felipeg86/Easyrun/Images/Aux Pines ESP.JPG

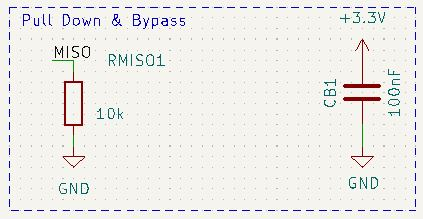
Images/Aux Pines ESP.JPG
