felipeg86/Easyrun/Images/Boost.png

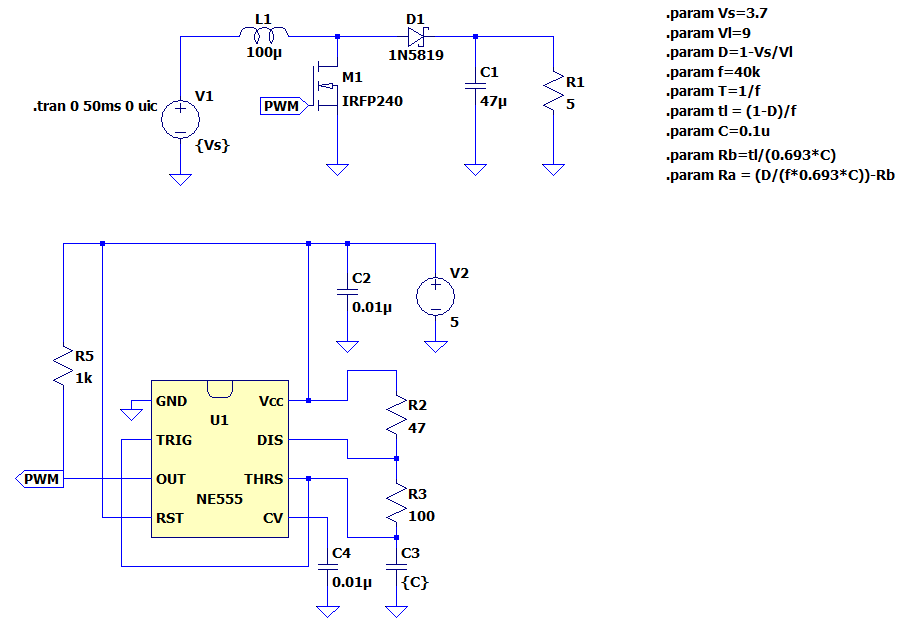
Images/Boost.png
