felipeg86/Easyrun/Images/Botones.JPG

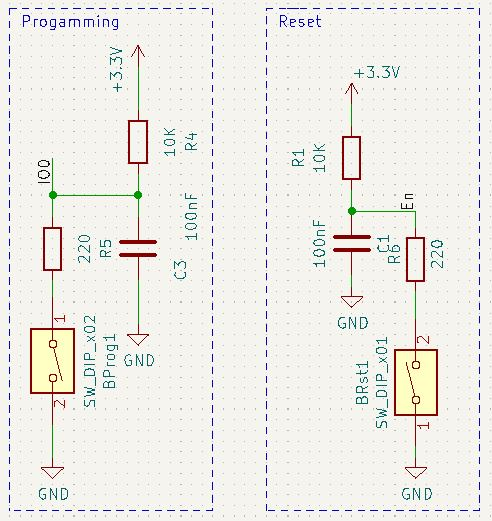
Images/Botones.JPG
