felipeg86/Easyrun/Images/Buck Diagram.png

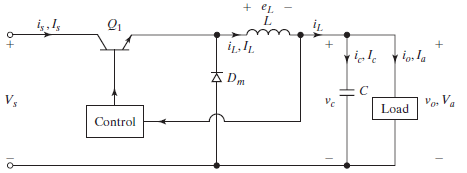
Images/Buck Diagram.png
