felipeg86/Easyrun/Images/Caja candado.jpg

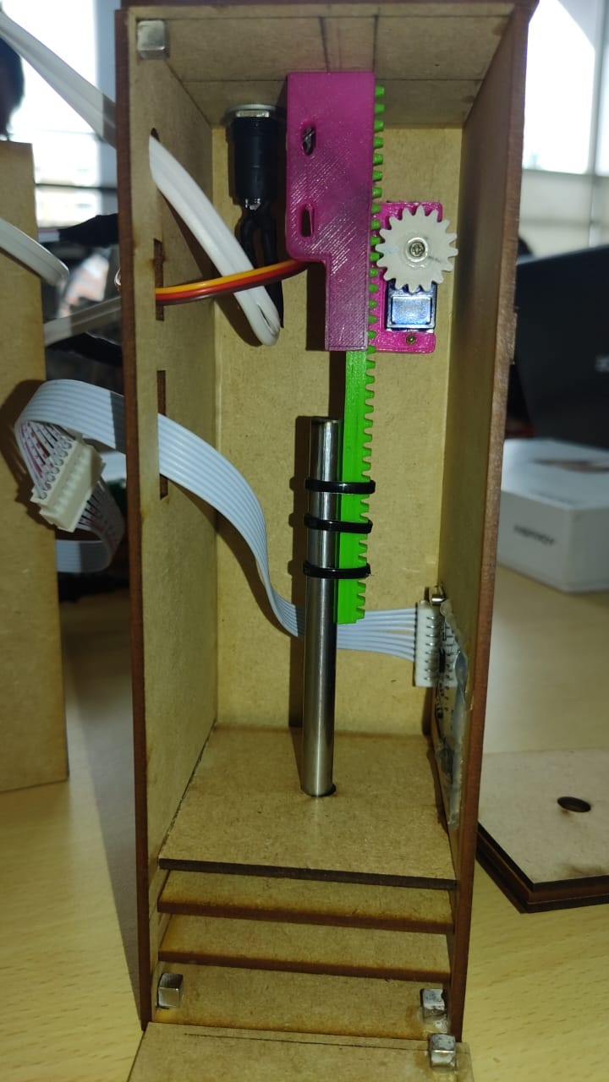
Images/Caja candado.jpg
