felipeg86/Easyrun/Images/caja con pcb.PNG

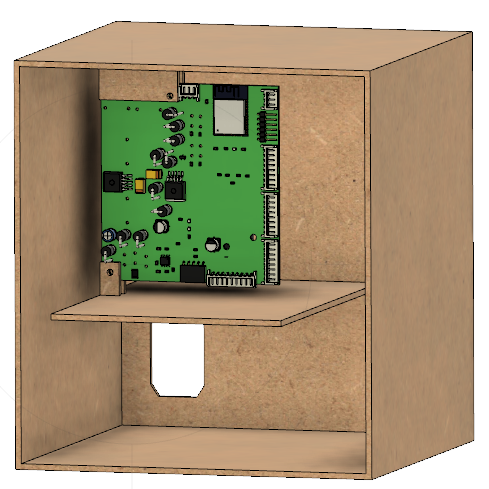
Images/caja con pcb.PNG
