felipeg86/Easyrun/Images/caja sin PCB.PNG

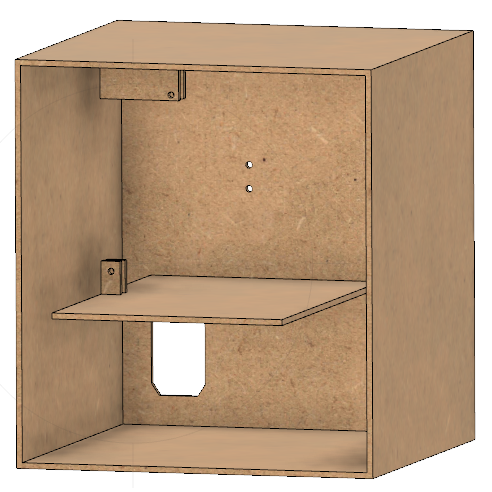
Images/caja sin PCB.PNG
