felipeg86/Easyrun/Images/Caja tarjeta.jpg

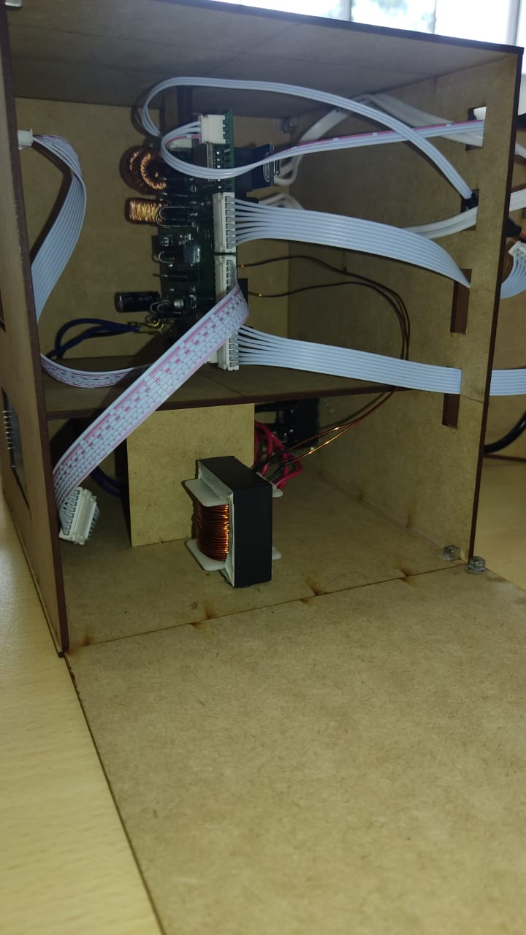
Images/Caja tarjeta.jpg
