felipeg86/Easyrun/Images/Carga.png

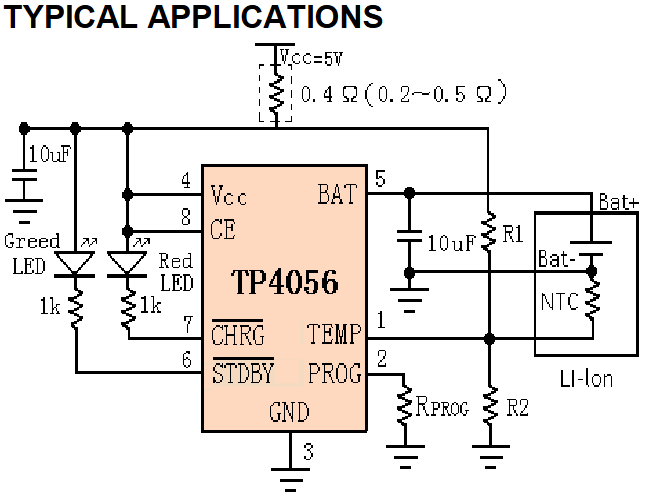
Images/Carga.png
