felipeg86/Easyrun/Images/Cargador_bateria.JPG

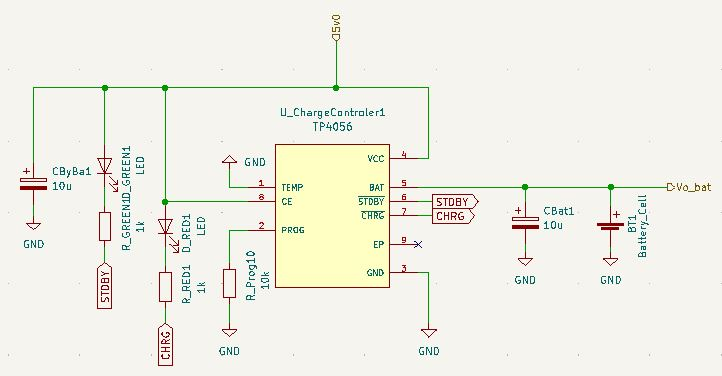
Images/Cargador_bateria.JPG
