felipeg86/Easyrun/Images/Controlador.png

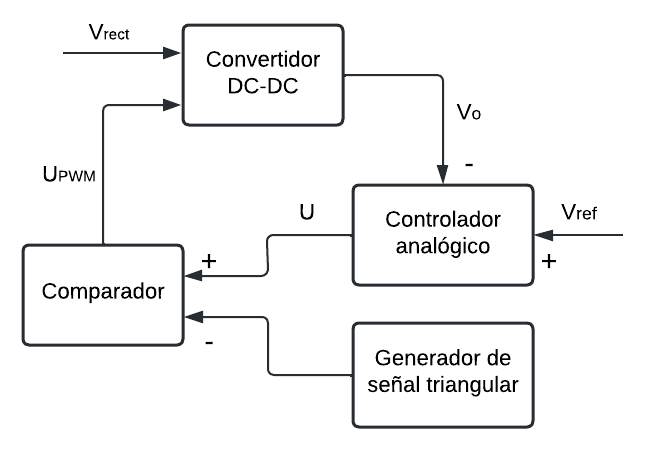
Images/Controlador.png
