felipeg86/Easyrun/Images/Convertidor 3.3.JPG

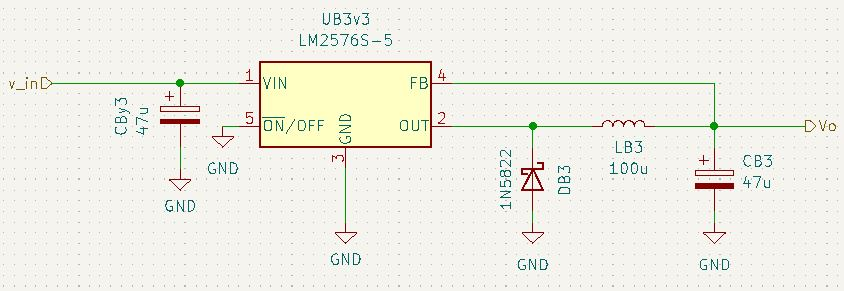
Images/Convertidor 3.3.JPG
