felipeg86/Easyrun/Images/Convertidor_bateria.JPG

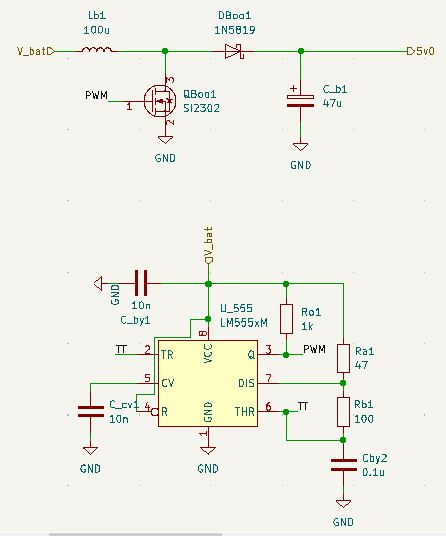
Images/Convertidor_bateria.JPG
