felipeg86/Easyrun/Images/Cuaderno sin título 2 P6.png

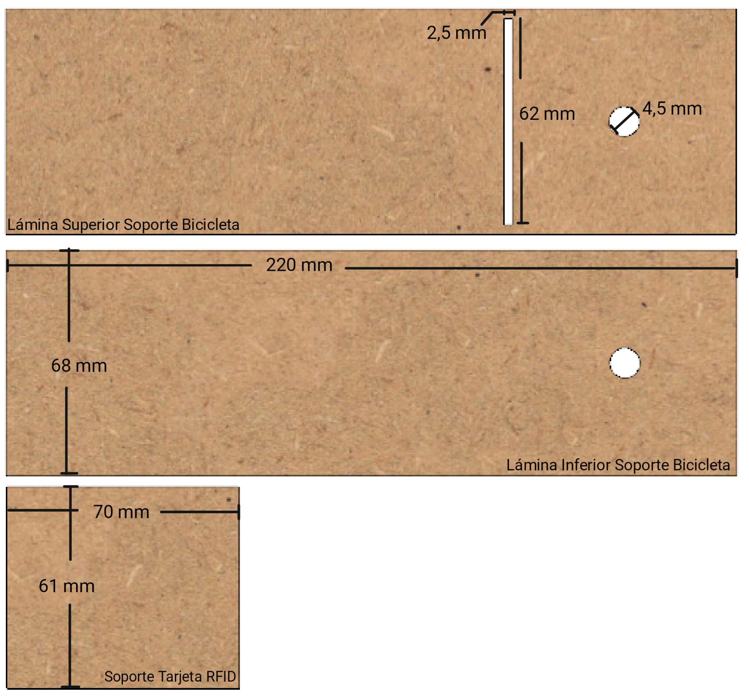
Images/Cuaderno sin título 2 P6.png
