felipeg86/Easyrun/Images/Diagrama Alimentacion.png

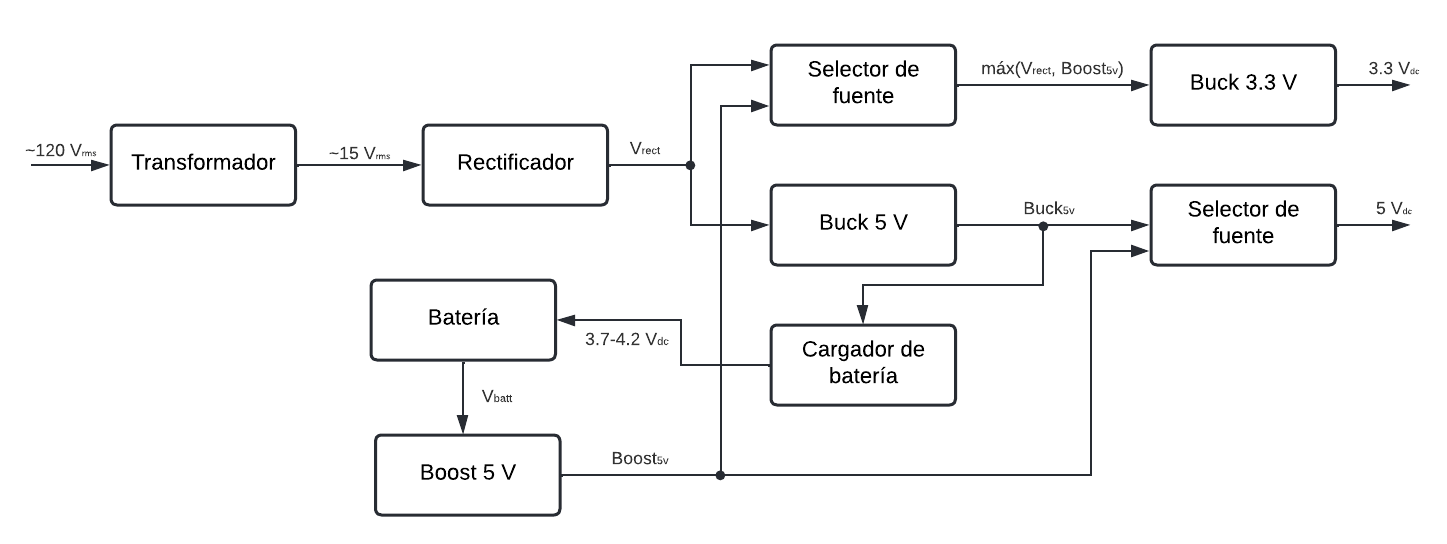
Images/Diagrama Alimentacion.png
