felipeg86/Easyrun/Images/Diagrama Buses.png

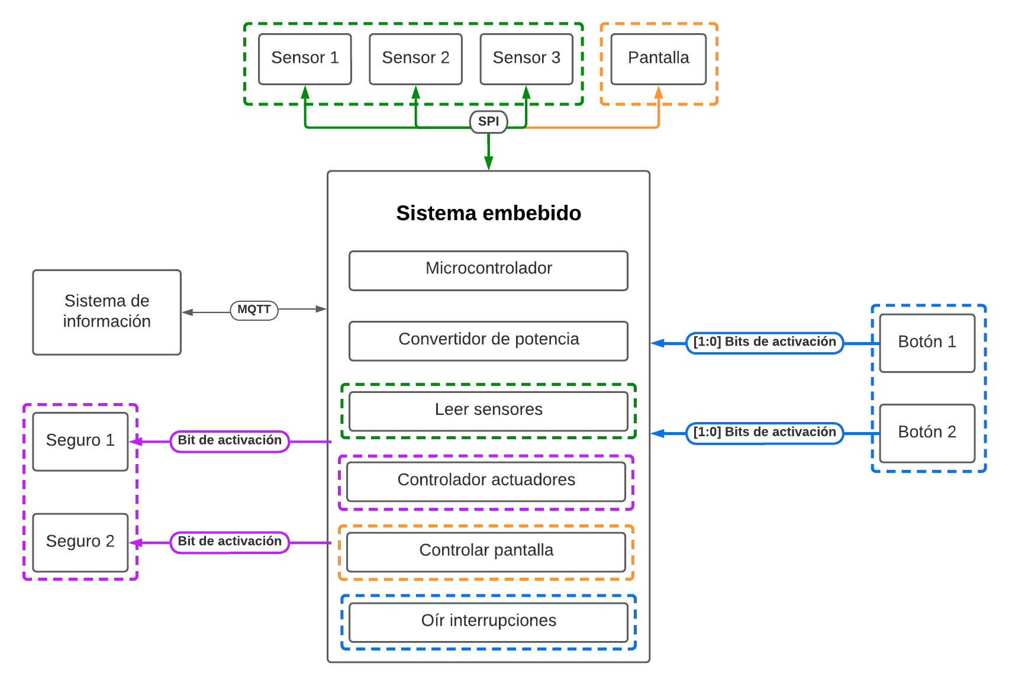
Images/Diagrama Buses.png
