felipeg86/Easyrun/Images/Diagrama coms - sencillo.jpg

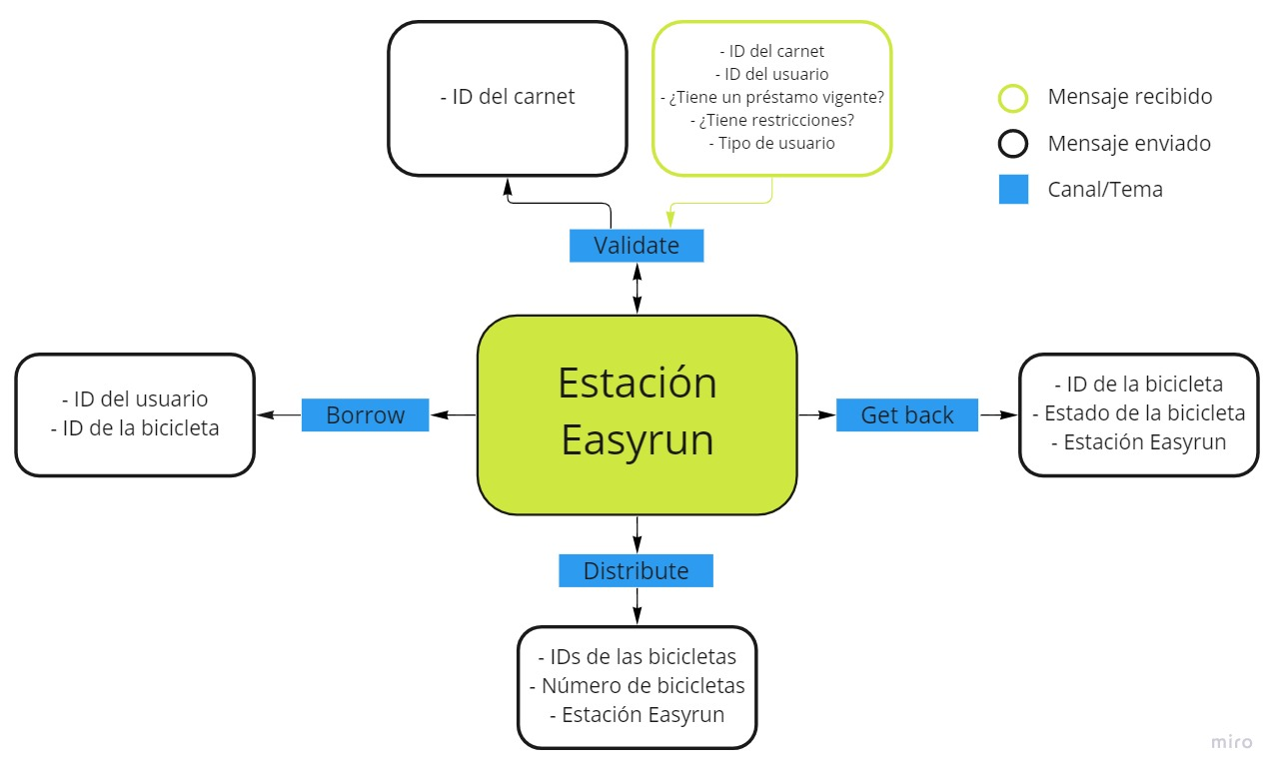
Images/Diagrama coms - sencillo.jpg
