felipeg86/Easyrun/Images/Diagrama de bloques_1.jpg

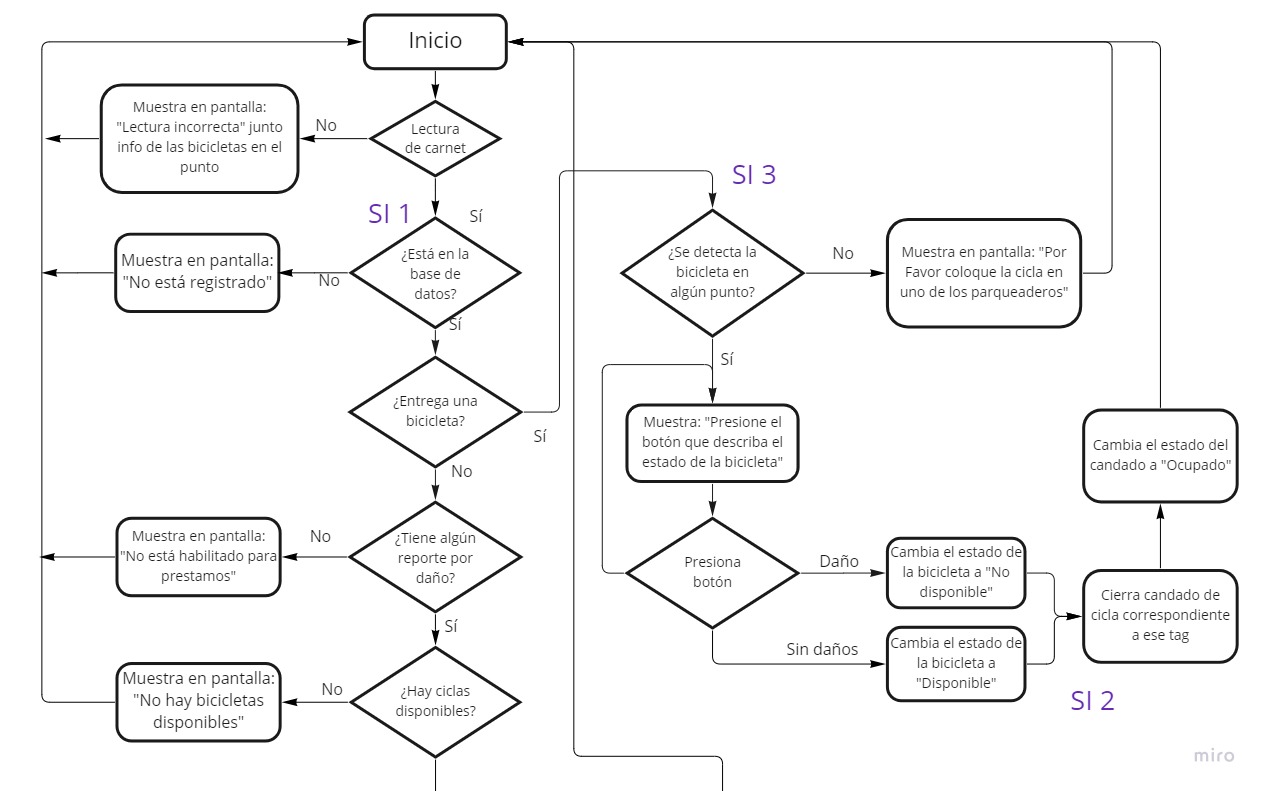
Images/Diagrama de bloques_1.jpg
