felipeg86/Easyrun/Images/Diagrama de bloques_2.jpg

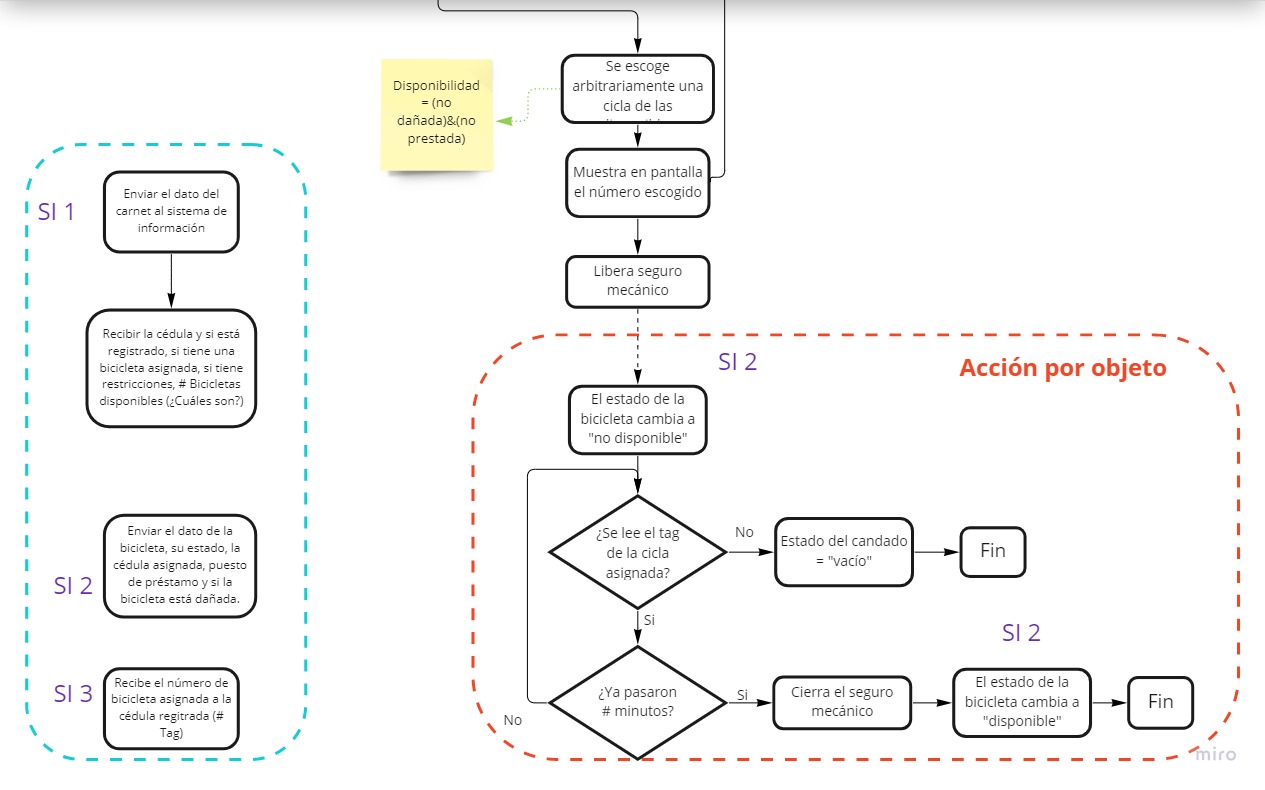
Images/Diagrama de bloques_2.jpg
