felipeg86/Easyrun/Images/Diagrama de bloques_3.jpg

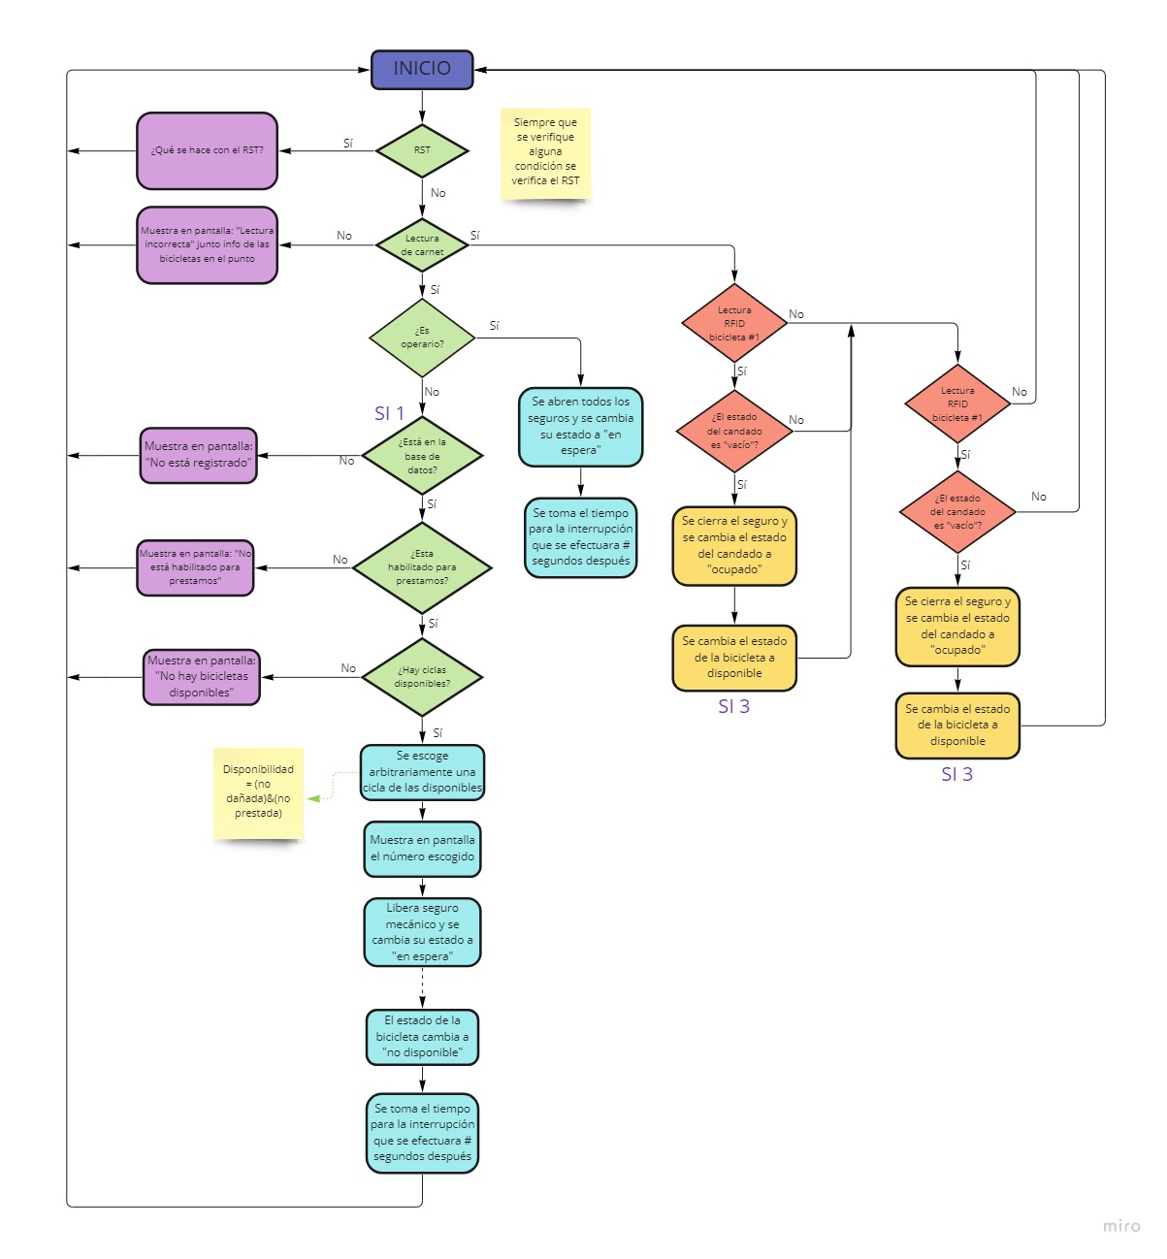
Images/Diagrama de bloques_3.jpg
