felipeg86/Easyrun/Images/Diagrama General.jpg

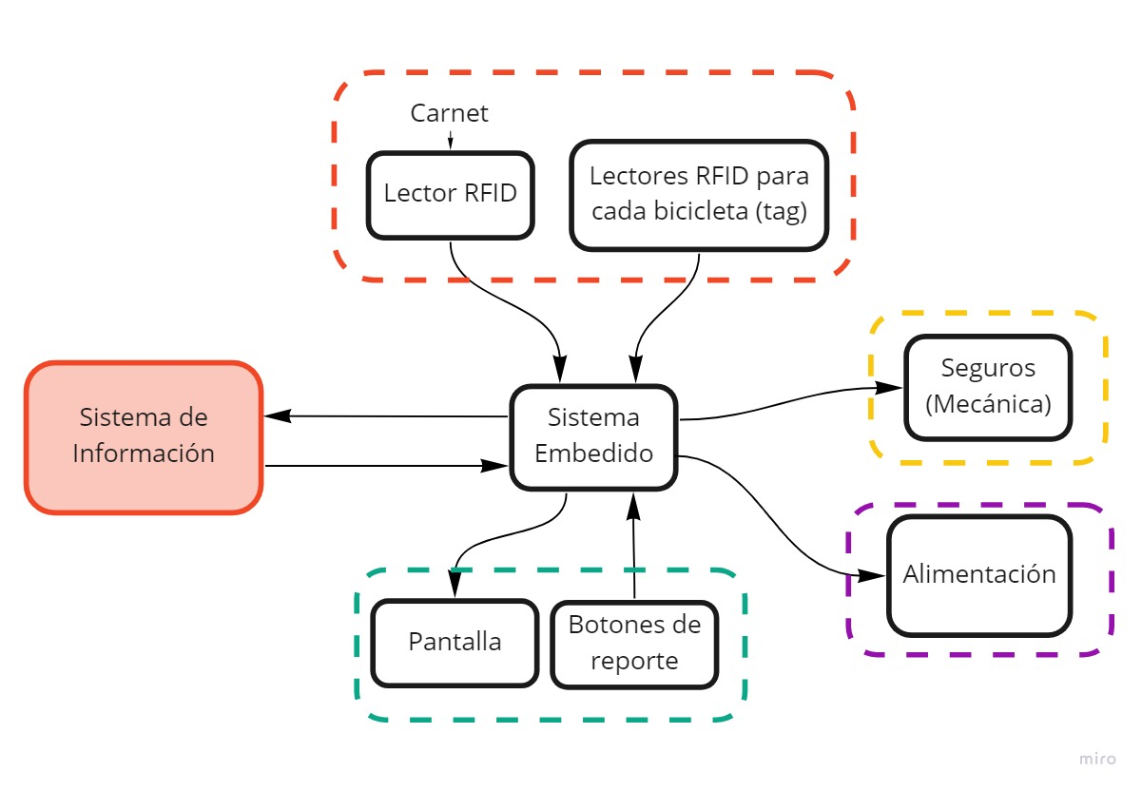
Images/Diagrama General.jpg
