felipeg86/Easyrun/Images/Diagrama sistema.png

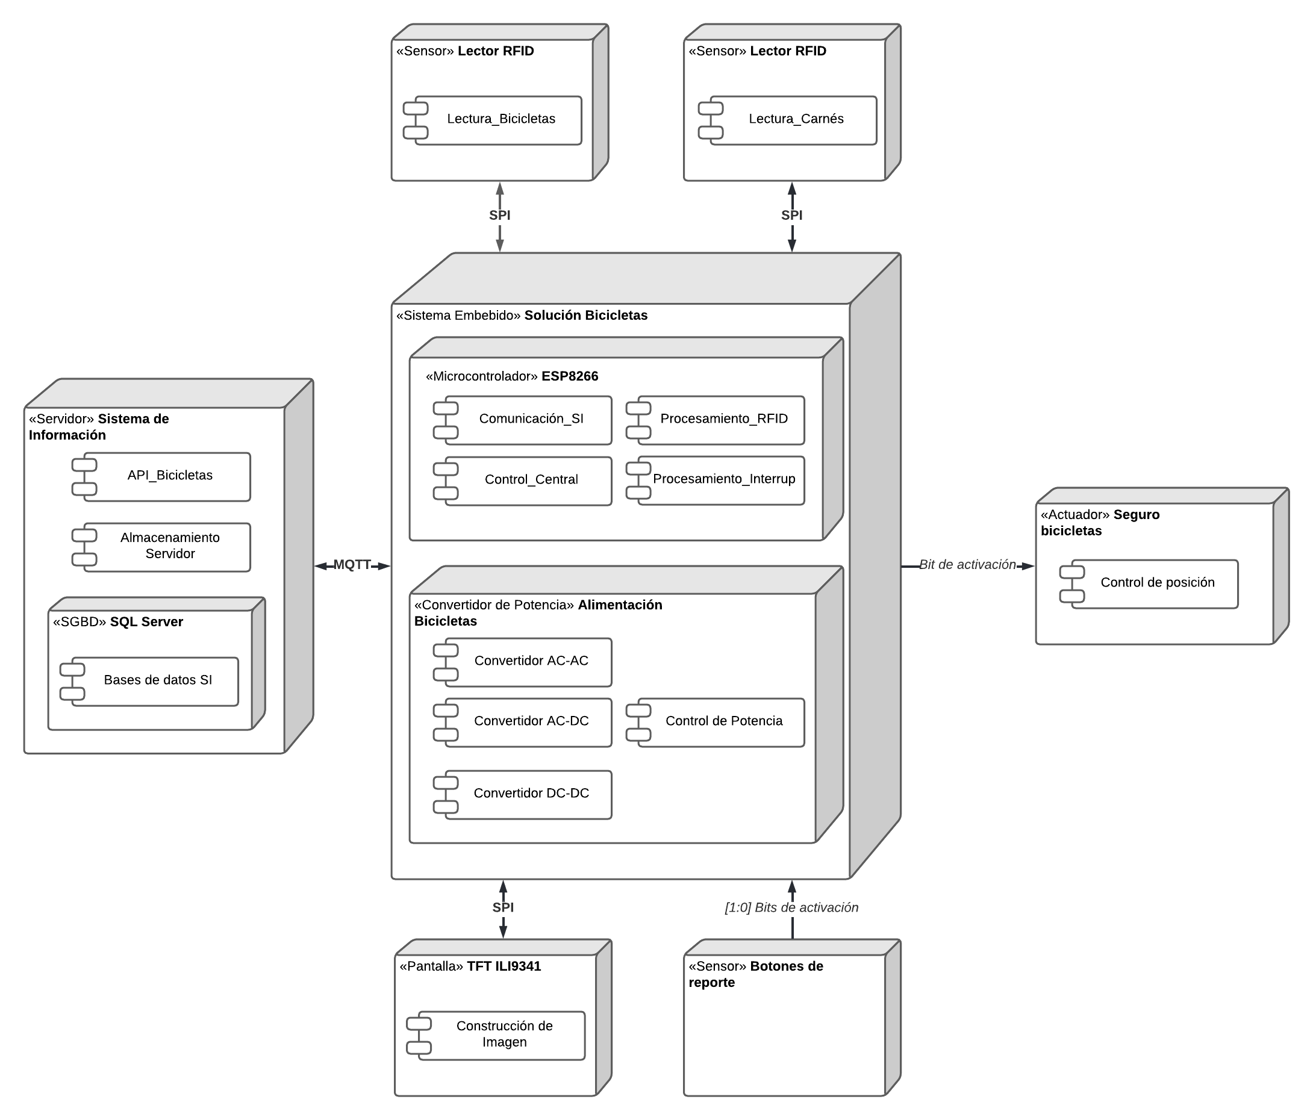
Images/Diagrama sistema.png
