felipeg86/Easyrun/Images/ESP32_esquema.JPG

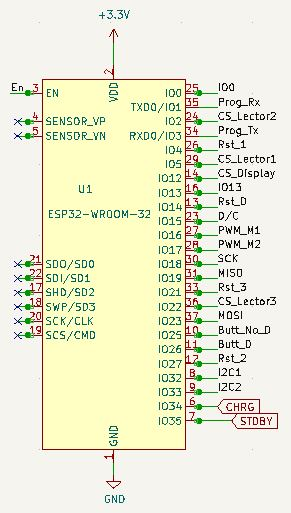
Images/ESP32_esquema.JPG
