felipeg86/Easyrun/Images/Estandar_IP.jpg

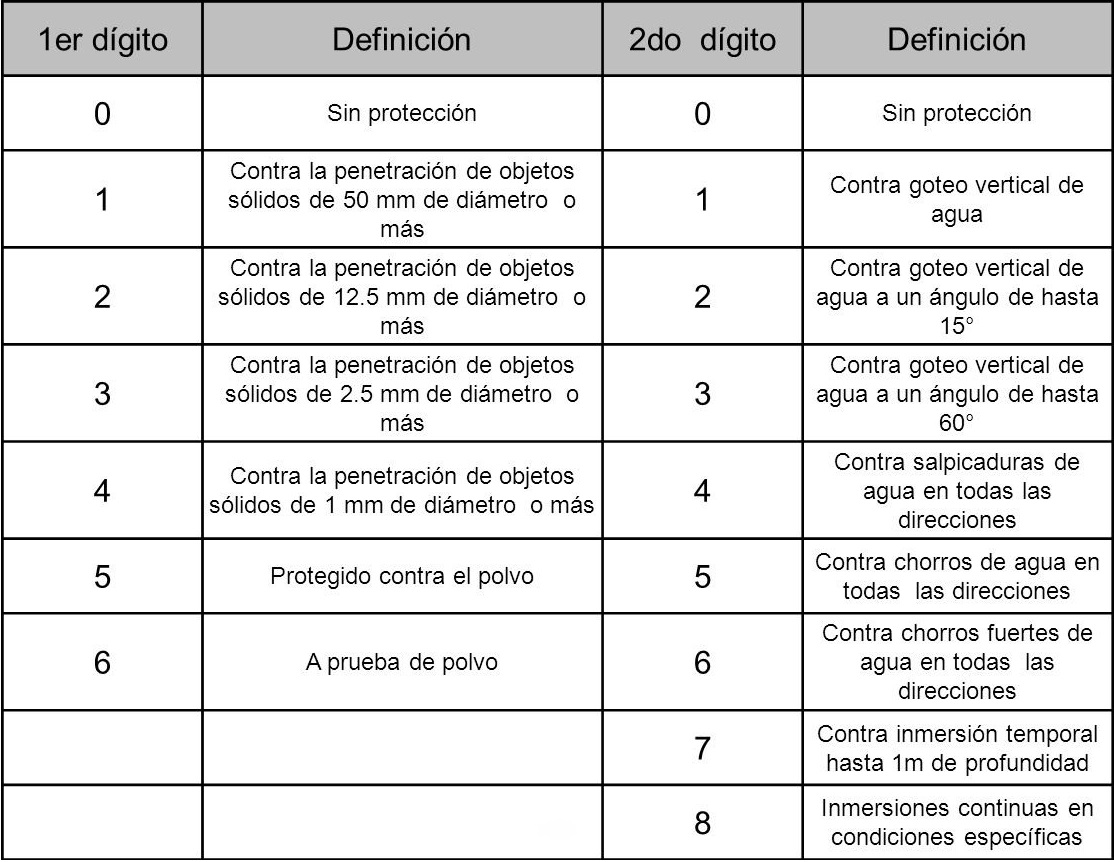
Images/Estandar_IP.jpg
