felipeg86/Easyrun/Images/Interacciones_SI.jpg

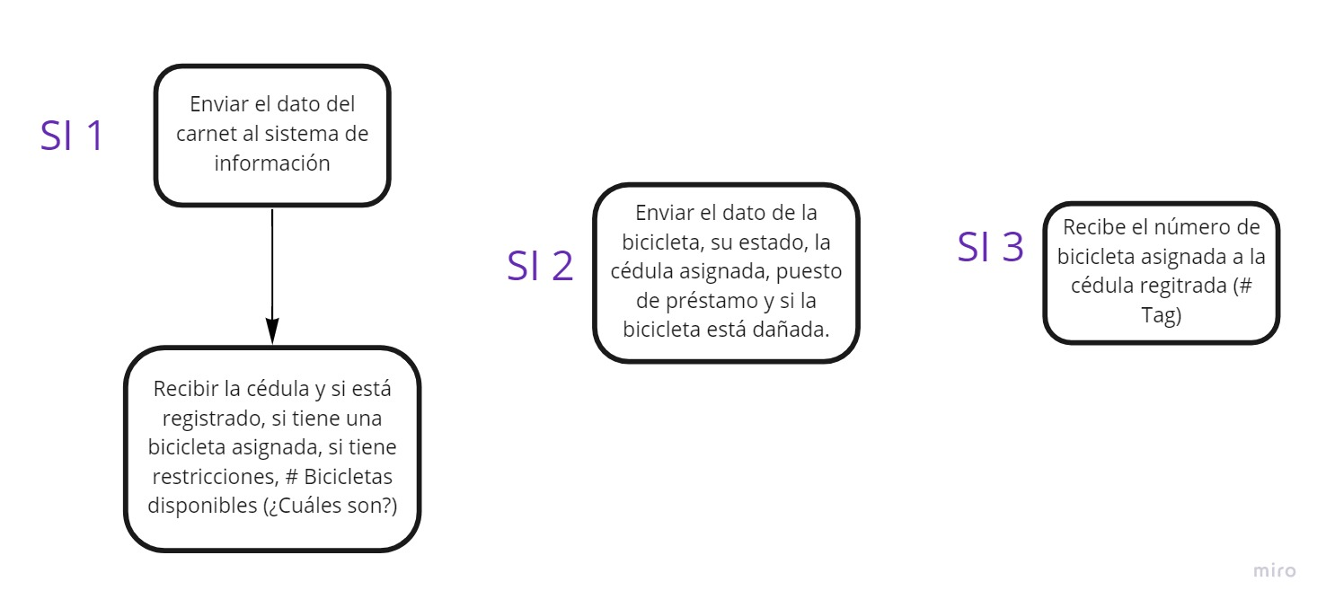
Images/Interacciones_SI.jpg
