felipeg86/Easyrun/Images/Interacciones_SI_1.jpg

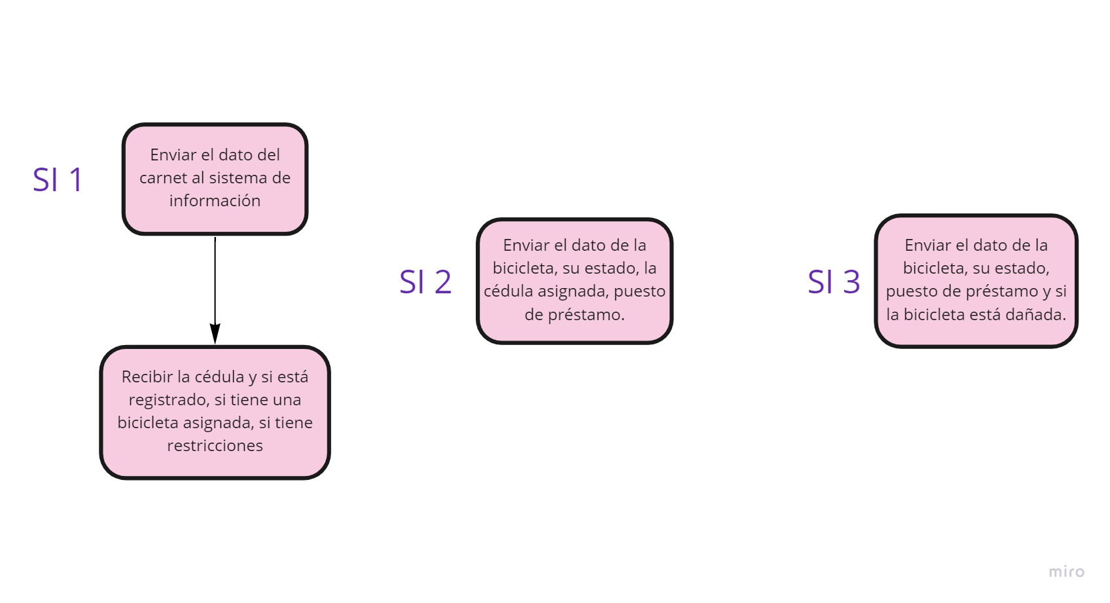
Images/Interacciones_SI_1.jpg
