felipeg86/Easyrun/Images/Interrupcion.jpg

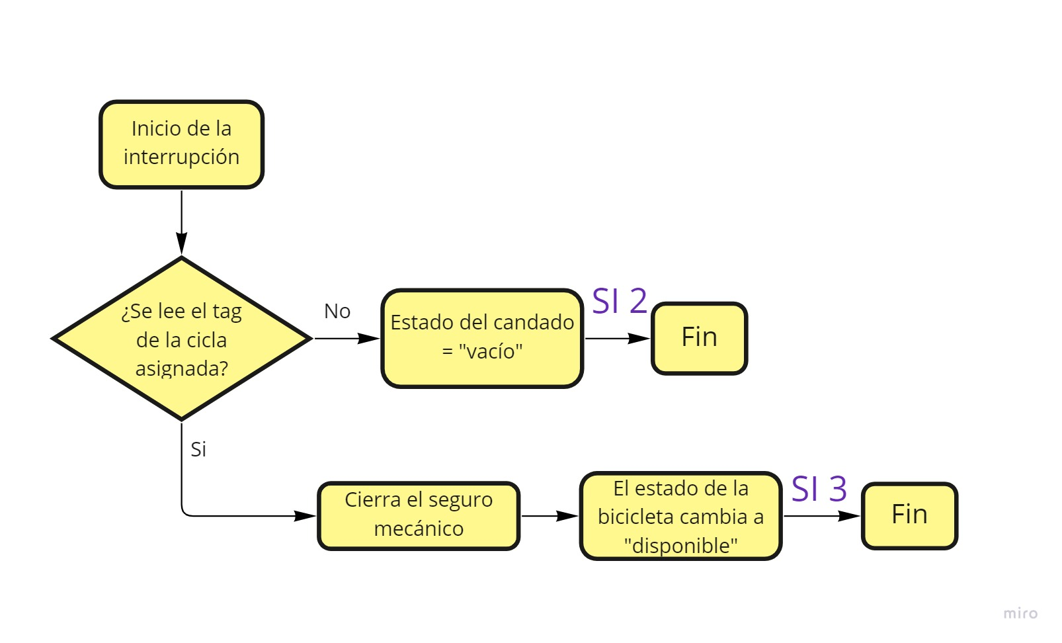
Images/Interrupcion.jpg
