felipeg86/Easyrun/Images/lateral cara superior inferior.png

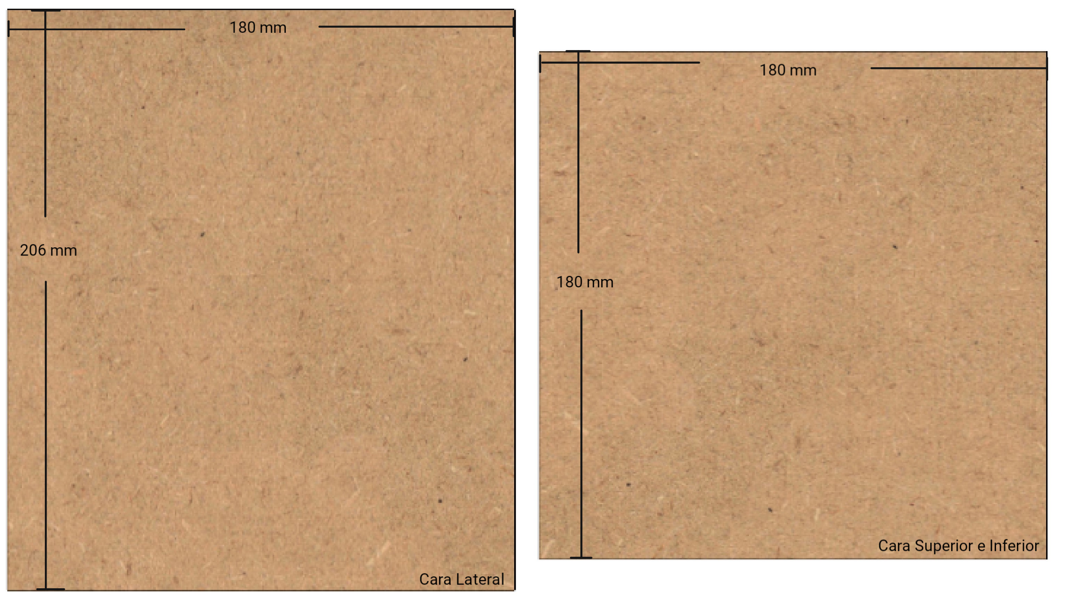
Images/lateral cara superior inferior.png
