felipeg86/Easyrun/Images/NEMA.jpg

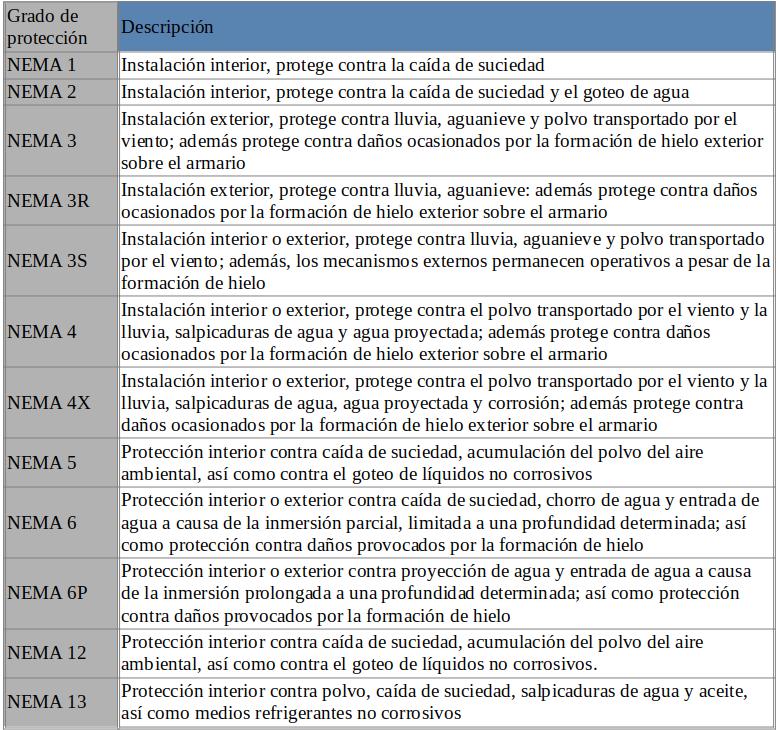
Images/NEMA.jpg
