felipeg86/Easyrun/Images/NTC positions.png

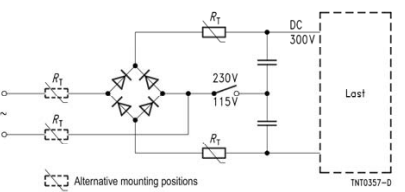
Images/NTC positions.png
