felipeg86/Easyrun/Images/PCB_down.JPG

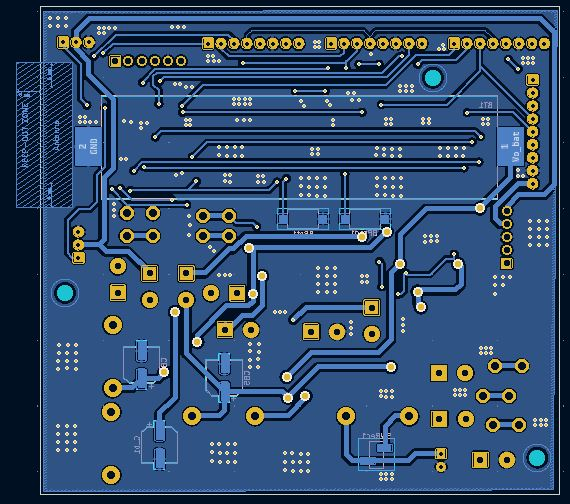
Images/PCB_down.JPG
