felipeg86/Easyrun/Images/PCB_up.JPG

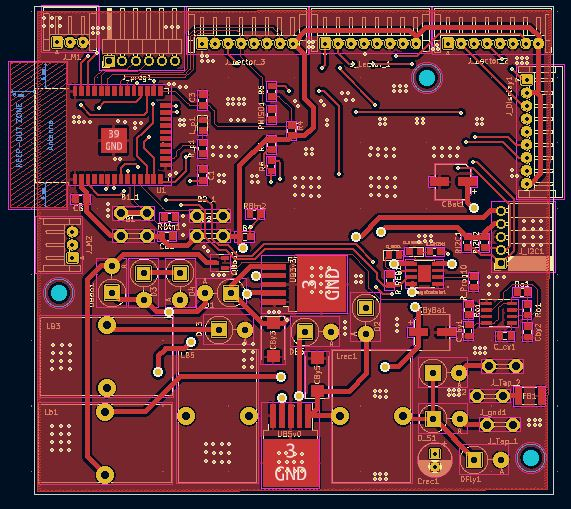
Images/PCB_up.JPG
