felipeg86/Easyrun/Images/Perifericos.JPG

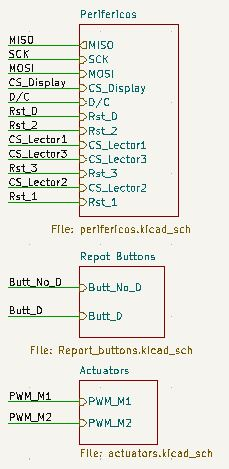
Images/Perifericos.JPG
