felipeg86/Easyrun/Images/Perifericos_lector_pantalla.JPG

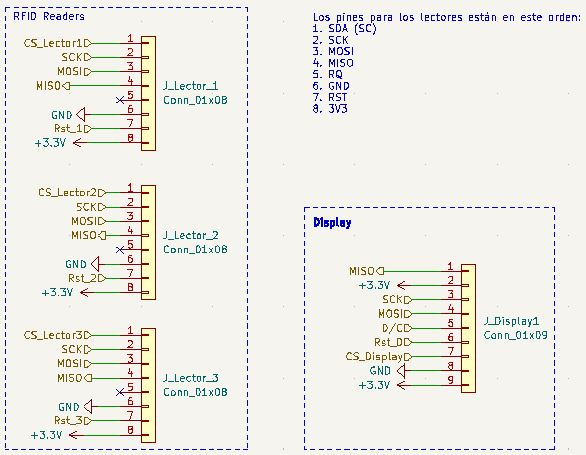
Images/Perifericos_lector_pantalla.JPG
