felipeg86/Easyrun/Images/picture_compress.gif

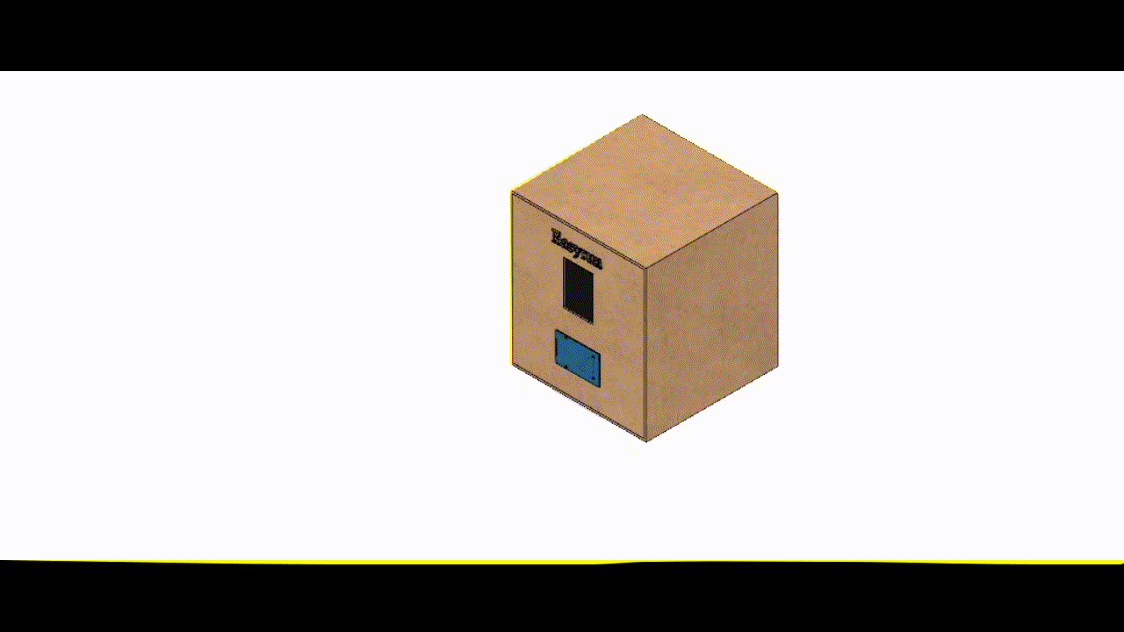
Images/picture_compress.gif
