felipeg86/Easyrun/Images/Potencia.JPG

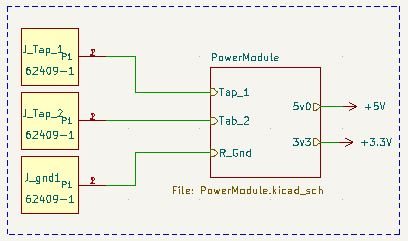
Images/Potencia.JPG
