felipeg86/Easyrun/Images/Potencia_Interno.JPG

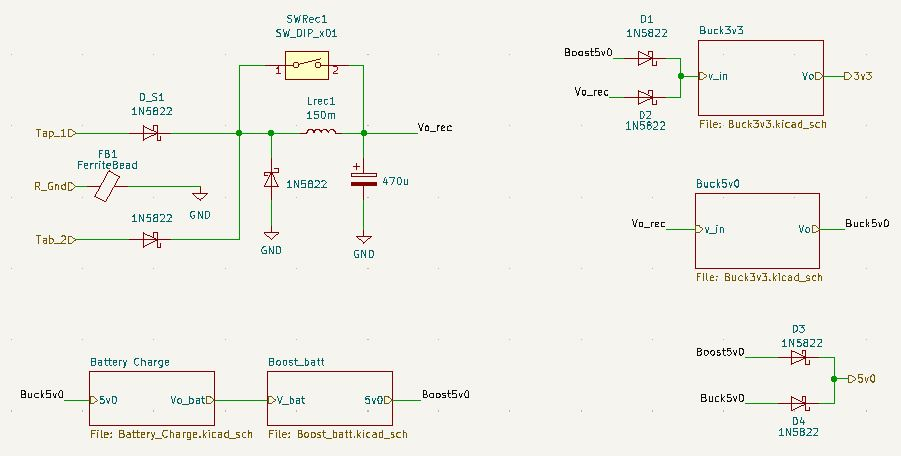
Images/Potencia_Interno.JPG
