felipeg86/Easyrun/Images/Programacion_interf_aux.JPG

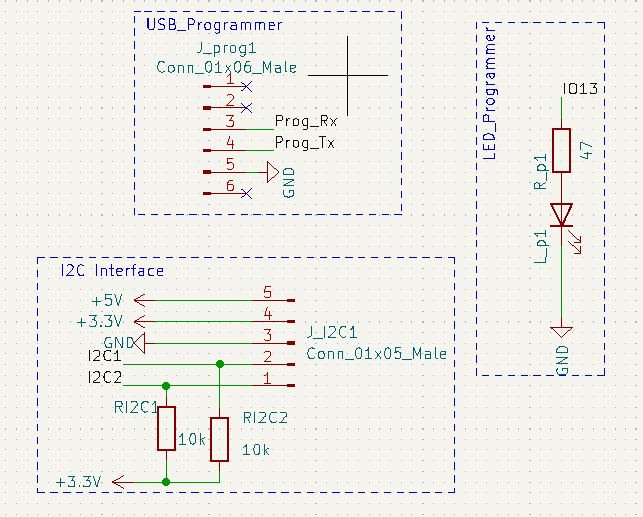
Images/Programacion_interf_aux.JPG
