felipeg86/Easyrun/Images/Rectificador_Final.png

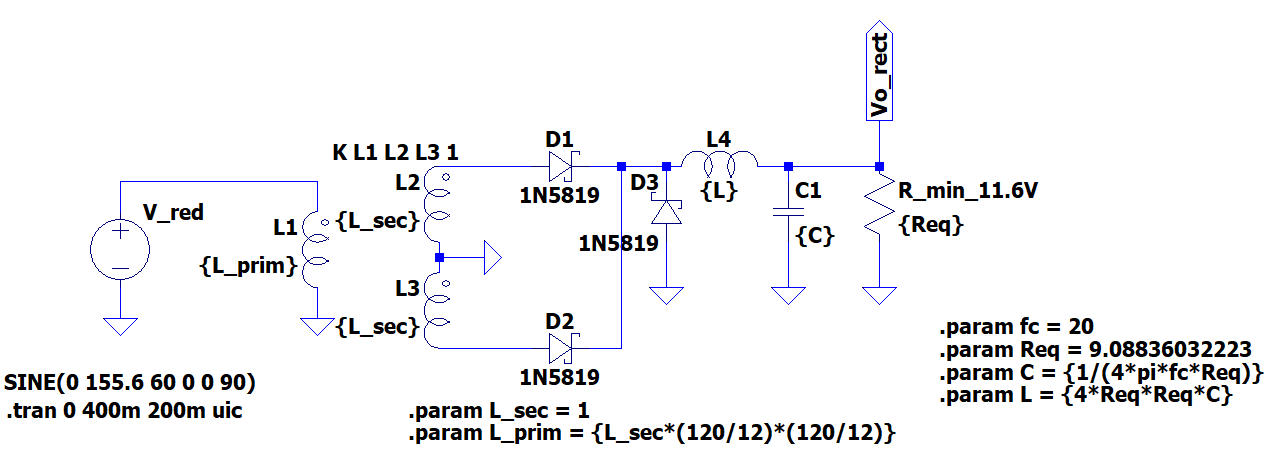
Images/Rectificador_Final.png
