felipeg86/Easyrun/Images/RFID_topo (2).jpeg

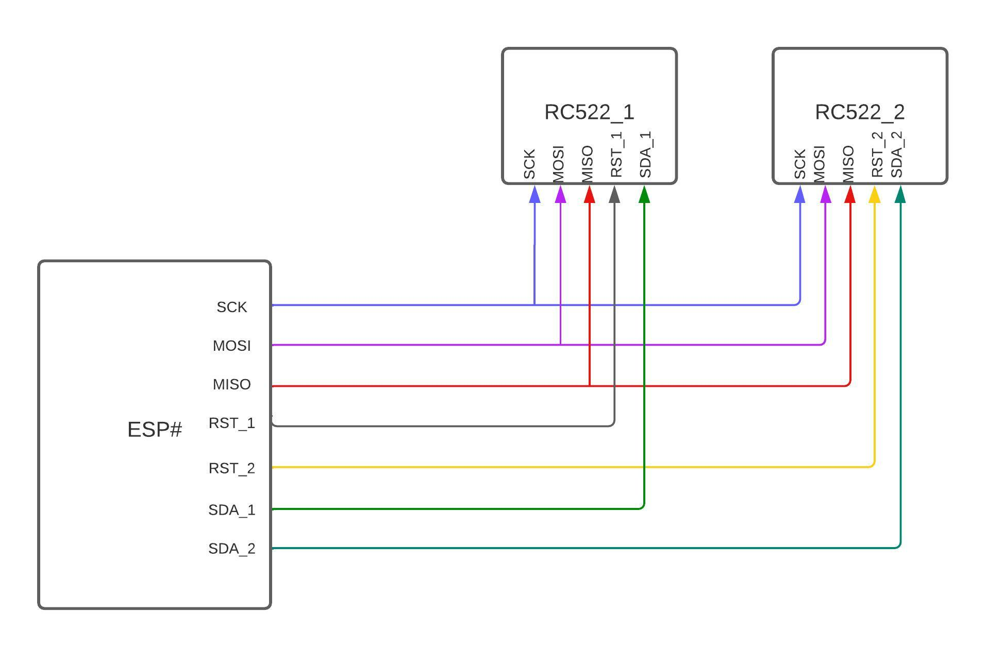
Images/RFID_topo (2).jpeg
