felipeg86/Easyrun/Images/SEGURO2 lateral superior inferior.png

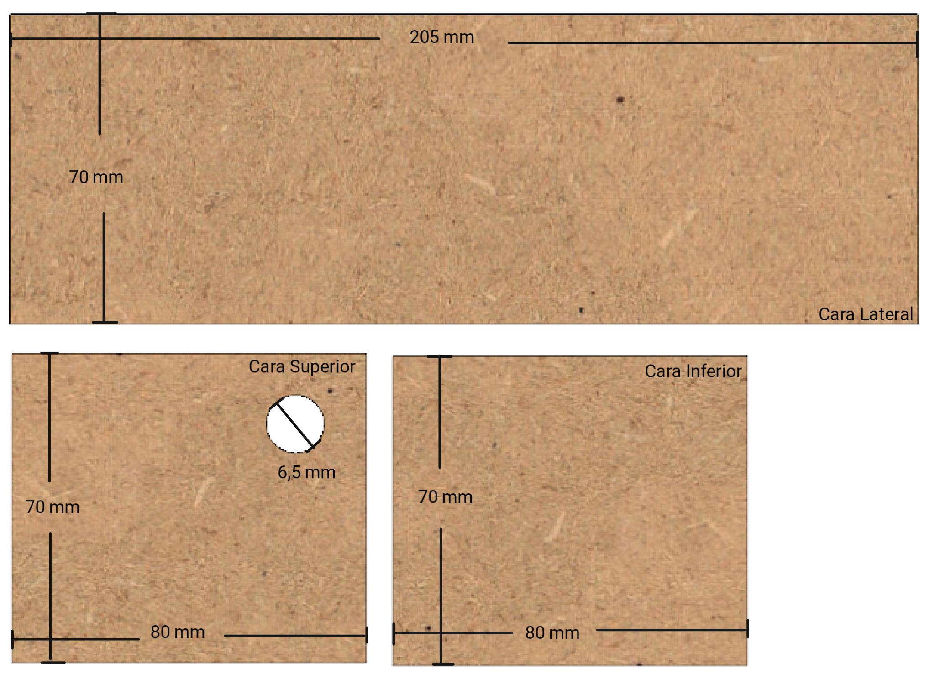
Images/SEGURO2 lateral superior inferior.png
