felipeg86/Easyrun/Images/SEGURO3 separador sujetador.png

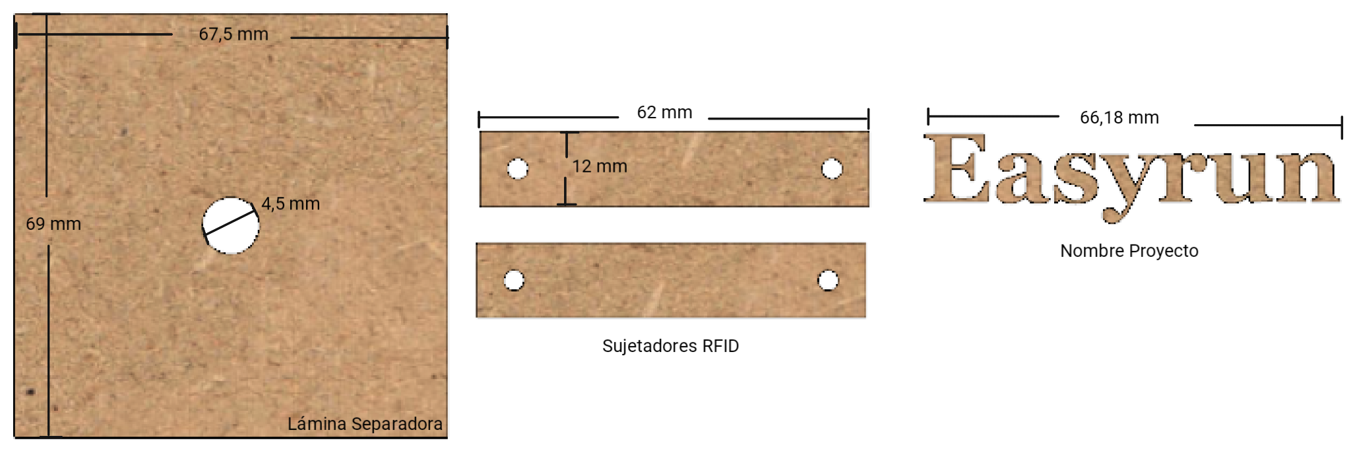
Images/SEGURO3 separador sujetador.png
