felipeg86/Easyrun/Images/senialTriang.png

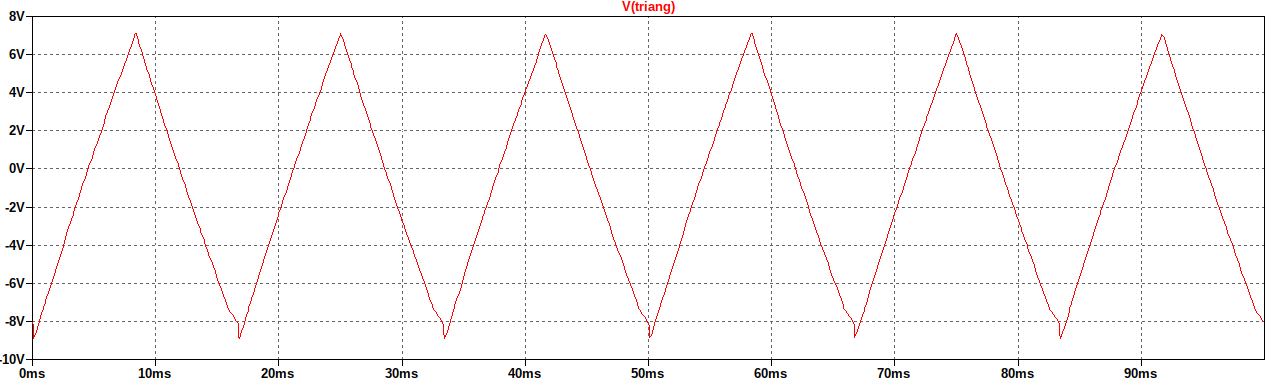
Images/senialTriang.png
