felipeg86/Easyrun/Images/separador sujetadores.png

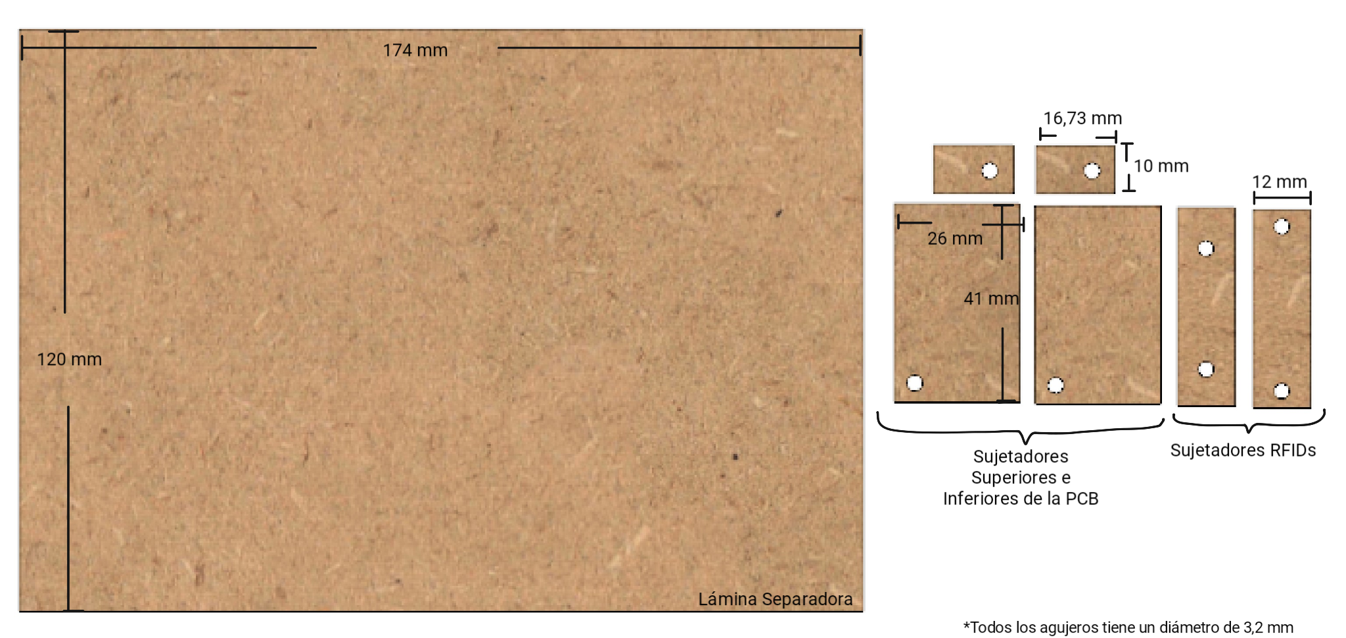
Images/separador sujetadores.png
