felipeg86/Easyrun/Images/Servomotores.JPG

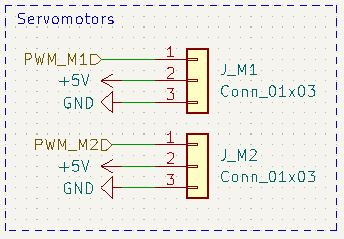
Images/Servomotores.JPG
