felipeg86/Easyrun/Images/SOPORTE SEGURO BICICLETA.PNG

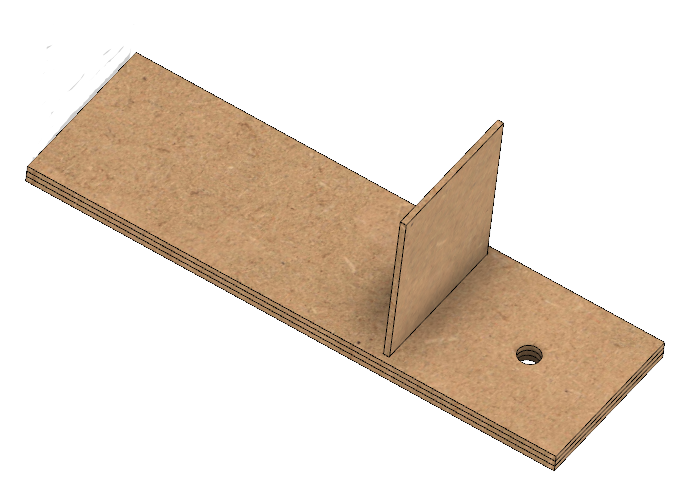
Images/SOPORTE SEGURO BICICLETA.PNG
