felipeg86/Easyrun/Images/Triang__.png

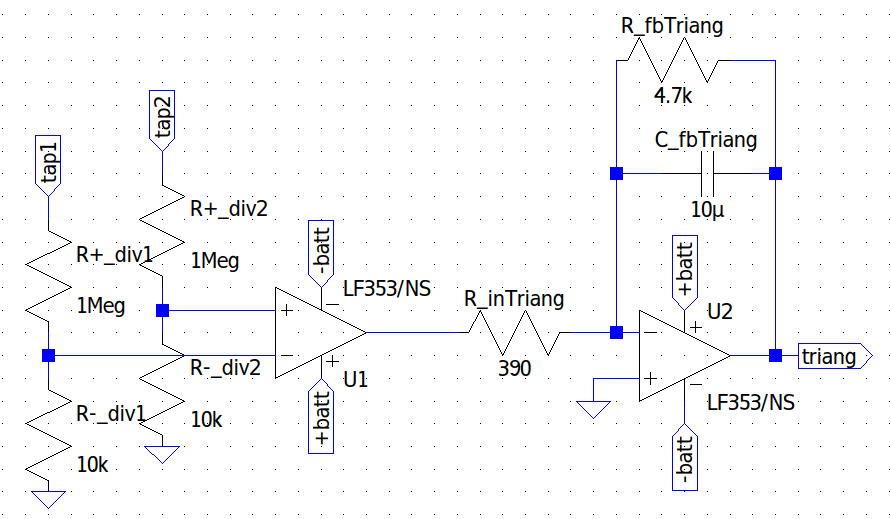
Images/Triang__.png
