felipeg86/Easyrun/Images/Vo-Io Buck I 5v.png

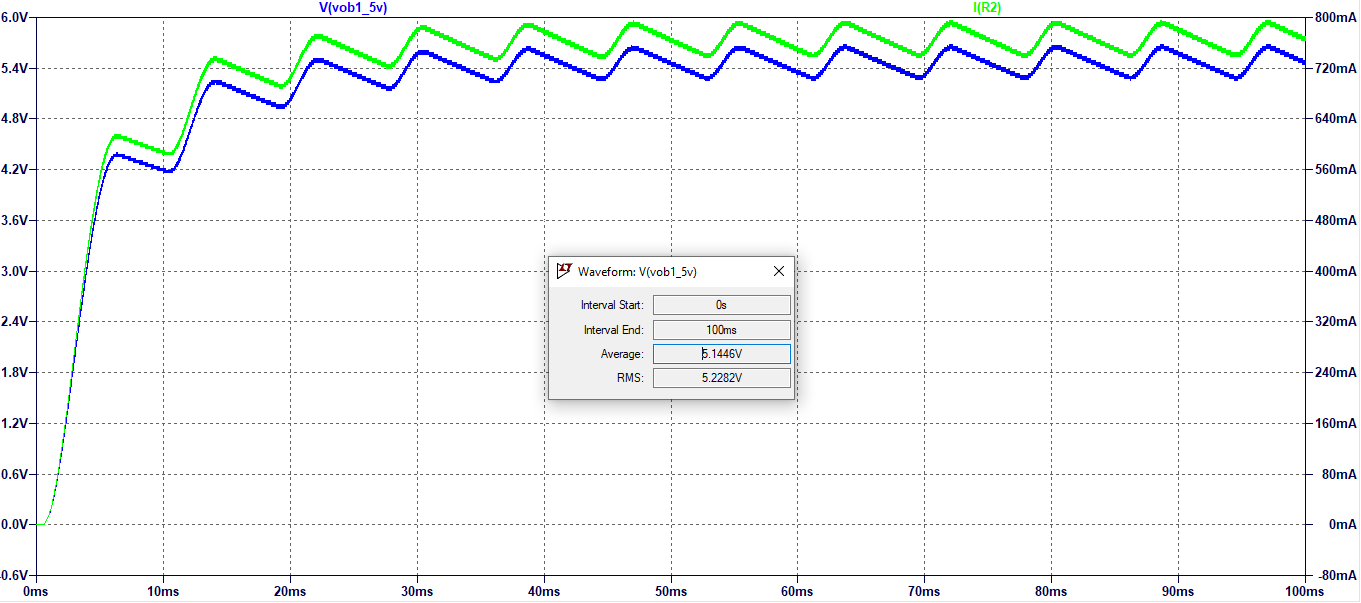
Images/Vo-Io Buck I 5v.png
