felipeg86/Easyrun/Images/Vo-Io Buck II 3v .png

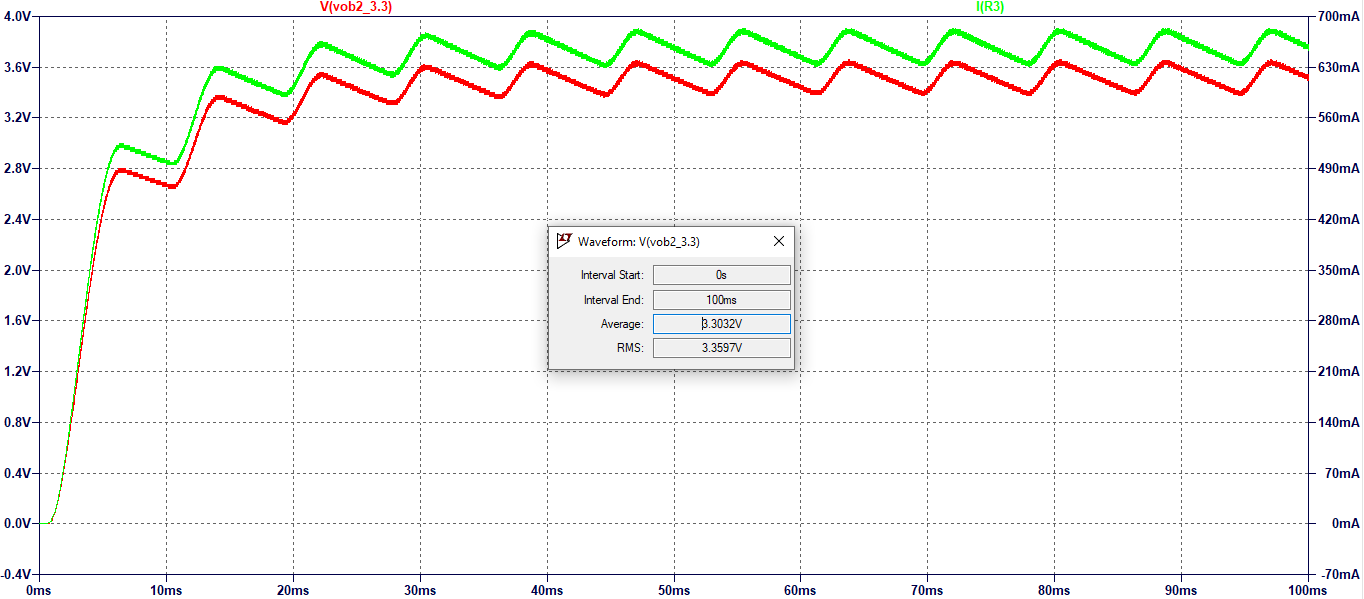
Images/Vo-Io Buck II 3v .png
