felipeg86/Easyrun/Images/Fabricación placa.jpeg

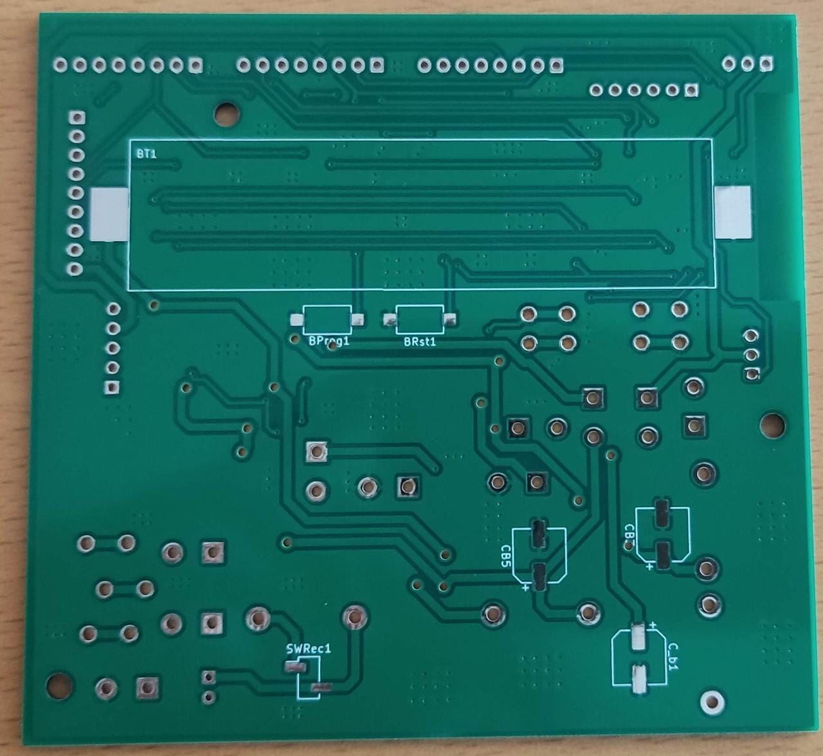
Images/Fabricación placa.jpeg
