felipeg86/Easyrun/Images/Pruebas Alimentación.png

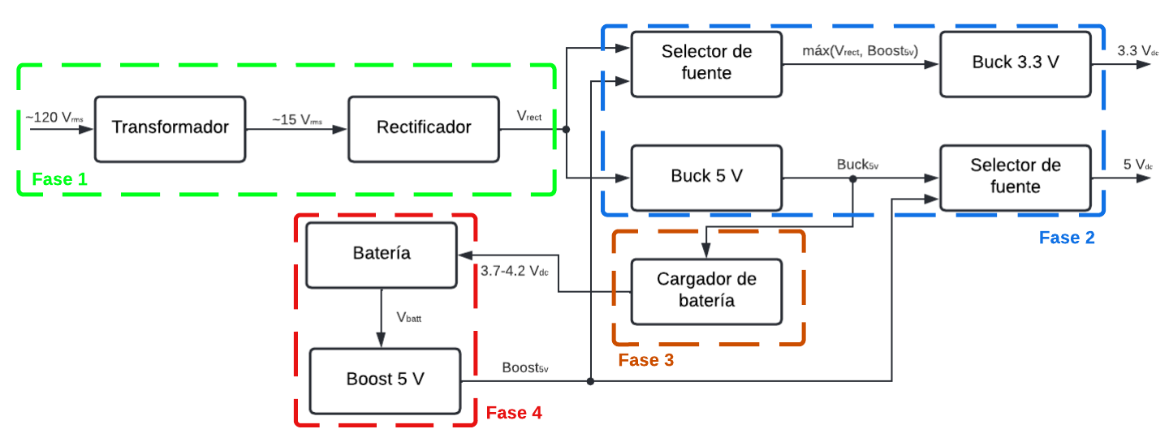
Images/Pruebas Alimentación.png
