felipeg86/Easyrun/Circuit Design/LTspice Simulations/Boost.asc

C1: cap; 47µ
C2: cap; 0.01µ
C3: cap; {C}
C4: cap; 0.01µ
D1: schottky; 1N5819
L1: ind; 100µ; Rser=56m
M1: nmos; IRFP240
R1: res; 5
R2: res; 47
R3: res; 100
R5: res; 1k
U1: NE555
V1: voltage; {Vs}
V2: voltage; 5
Named nets: 0, PWM
.param f=40k
.param T=1/f
.param Vs=3.7
.param Vl=9
.param D=1-Vs/Vl
.tran 0 50ms 0 uic
.param tl = (1-D)/f
.param Rb=tl/(0.693*C)
.param C=0.1u
.param Ra = (D/(f*0.693*C))-Rb
