felipeg86/Easyrun/Circuit Design/LTspice Simulations/PowerModule.asc

C1: cap; 47µ
C2: cap; {C}
C3: cap; 47µ
D1: diode
D2: diode
D3: diode
D4: diode
D5: diode
L1: ind2; 100µ
L2: ind2; {L_prim}; Rser=1
L3: ind2; {L_sec}
L4: ind2; {L_sec}
L5: ind; {L}; Rser=0.4
L6: ind2; 100µ
R1: res; 5.35
R2: res; {2k*(3.3/1.23 - 1)}
R3: res; 2k
R4: res; 3.57
R5: res; {2k*(5/1.23 - 1)}
R6: res; 2k
U1: LM2576_TRANS
U2: LM2576_TRANS
V_red1: voltage; SINE(0 155.6 60 0 0 90)
Named nets: 0, Vo_rect
K L1 L2 L3 1
.tran 0 300m 100m uic
.param C = {100u}
.param L = {150m}
.param fc = 20
.param L_sec = 1
.param L_prim = {L_sec*(120/12)*(120/12)}
.param Req = 9.08836032223
