felipeg86/Easyrun/Circuit Design/LTspice Simulations/Buck3v3.asc

C1: cap; 47µ
D1: schottky; 1N5819
L1: ind; 100µ
R1: res; 5.35
R2: res; {2k*(3.3/1.23 - 1)}
R3: res; 2k
U1: LM2576_TRANS
V1: voltage; SINE(9.0624 {1*185m} 120)
Named nets: 0
.tran 20m uic
