felipeg86/Easyrun/Circuit Design/LTspice Simulations/Rectifier.asc

C1: cap; {C}
D1: schottky; 1N5819
D2: schottky; 1N5819
D3: schottky; 1N5819
L1: ind2; {L_prim}; Rser=1
L2: ind2; {L_sec}
L3: ind2; {L_sec}
L4: ind; {L}; Rser=0.4
R_min_11.6V: res; {Req}
V_red: voltage; SINE(0 155.6 60 0 0 90)
Named nets: 0, Vo_rect
K L1 L2 L3 1
.tran 0 400m 200m uic
.param Req = 9.08836032223
.param C = {1/(4*pi*fc*Req)}
.param L = {4*Req*Req*C}
.param fc = 20
.param L_sec = 1
.param L_prim = {L_sec*(120/12)*(120/12)}
