felipeg86/Easyrun/Micropython/Display/img2rgb565.py

"""Utility to convert images to raw RGB565 format."""

from PIL import Image
from struct import pack
from os import path
import sys


def error(msg):
    """Display error and exit."""
    print (msg)
    sys.exit(-1)


def write_bin(f, pixel_list):
    """Save image in RGB565 format."""
    for pix in pixel_list:
        r = (pix[0] >> 3) & 0x1F
        g = (pix[1] >> 2) & 0x3F
        b = (pix[2] >> 3) & 0x1F
        f.write(pack('>H', (r << 11) + (g << 5) + b))


if __name__ == '__main__':
    args = sys.argv
    if len(args) != 2:
        error('Please specify input file: ./img2rgb565.py test.png')
    in_path = args[1]
    if not path.exists(in_path):
        error('File Not Found: ' + in_path)

    filename, ext = path.splitext(in_path)
    out_path = filename + '.raw'
    img = Image.open(in_path).convert('RGB')
    pixels = list(img.getdata())
    with open(out_path, 'wb') as f:
        write_bin(f, pixels)
    print('Saved: ' + out_path)
