felipeg86/Easyrun/Micropython/Skeleton/Archivos_ESP/Perifericos.py

from mfrc522 import MFRC522
from machine import Pin
from machine import SPI
from machine import SoftSPI
from machine import PWM

from ili9341 import Display, color565
from xglcd_font import XglcdFont
import math
import time

sck=18
mosi=23
miso=19

spi=SoftSPI(baudrate=200000, polarity=0, phase=0, sck=Pin(sck, Pin.OUT), mosi=Pin(mosi, Pin.OUT), miso=Pin(miso, Pin.OUT))
spi.init()

rdr1 = MFRC522(spi=spi, gpioRst=4, gpioCs=5)
rdr2 = MFRC522(spi=spi, gpioRst=27, gpioCs=2)
rdr3 = MFRC522(spi=spi, gpioRst=21, gpioCs=22)

def get_spi():
    return spi

def lectura(numero_lector):

    print("Place card")

    card_id="0"
    if(numero_lector==1):
        for i in range(1,10):
            (stat, tag_type) = rdr1.request(rdr1.REQIDL)
            if stat == rdr1.OK:    
                (stat, raw_uid) = rdr1.anticoll()
                if stat == rdr1.OK:
                    card_id = "0x%02x%02x%02x%02x" % (raw_uid[0], raw_uid[1], raw_uid[2], raw_uid[3])
                    return card_id
    elif(numero_lector==2):
        for i in range(1,10):
            (stat, tag_type) = rdr2.request(rdr2.REQIDL)
            if stat == rdr2.OK:    
                (stat, raw_uid) = rdr2.anticoll()
                if stat == rdr2.OK:
                    card_id = "0x%02x%02x%02x%02x" % (raw_uid[0], raw_uid[1], raw_uid[2], raw_uid[3])
                    return card_id

    elif(numero_lector==3):
        for i in range(1,10):
            (stat, tag_type) = rdr3.request(rdr3.REQIDL)
            if stat == rdr3.OK:    
                (stat, raw_uid) = rdr3.anticoll()
                if stat == rdr3.OK:
                    card_id = "0x%02x%02x%02x%02x" % (raw_uid[0], raw_uid[1], raw_uid[2], raw_uid[3])
                    return card_id

    else:
        card_id="0"
        print("error")
        return card_id


def servo_open(num_servo):
    if num_servo == 1:
        servo = PWM(Pin(16))
        servo.freq(50)  #Hz
        for j in range (120,20,-5):
            servo.duty(j)
            time.sleep_ms(50)
        servo.duty(0)
    elif num_servo == 2:
        servo = PWM(Pin(17))  #configurar pin 21 para trabajar con PWM
        servo.freq(50)  #Hz
        for j in range (120,20,-5):
            servo.duty(j)
            time.sleep_ms(50)
        servo.duty(0)
        servo.duty(0)

def servo_close(num_servo):
    if num_servo == 1:
        servo = PWM(Pin(16))  #configurar pin 21 para trabajar con PWM
        servo.freq(50)  #Hz
        for j in range (20,120,5):
            servo.duty(j)
            time.sleep_ms(50)
        servo.duty(0)
    elif num_servo == 2:
        servo = PWM(Pin(17))  #configurar pin 21 para trabajar con PWM
        servo.freq(50)  #Hz
        for j in range (20,120,5):
            servo.duty(j)
            time.sleep_ms(50)
        servo.duty(0)
    


"""
About printing text:
* 14 is recommended as difference between two lines 'y' coordinates for broadway font.
* 10 is recommended as difference between two characters 'x' coordinates for broadway font.
* A maximum of 23 characters (letters and numbers) can be printed per line
* 10*23=230 spaces in one line
"""
